developedby/Robo-Sugador/modelagem/hw/esq-motores.png

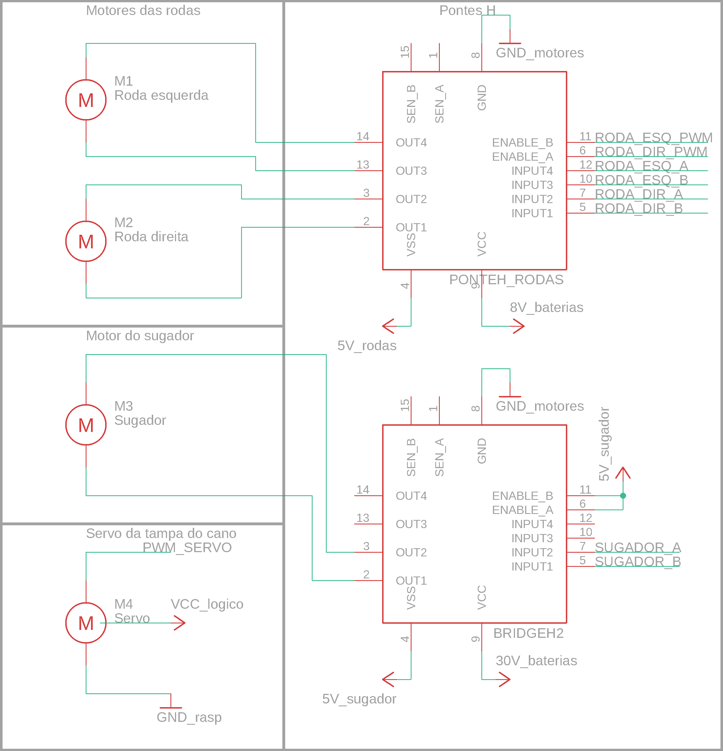
modelagem/hw/esq-motores.png
