developedby/Robo-Sugador/modelagem/hw/esq-rasp.png

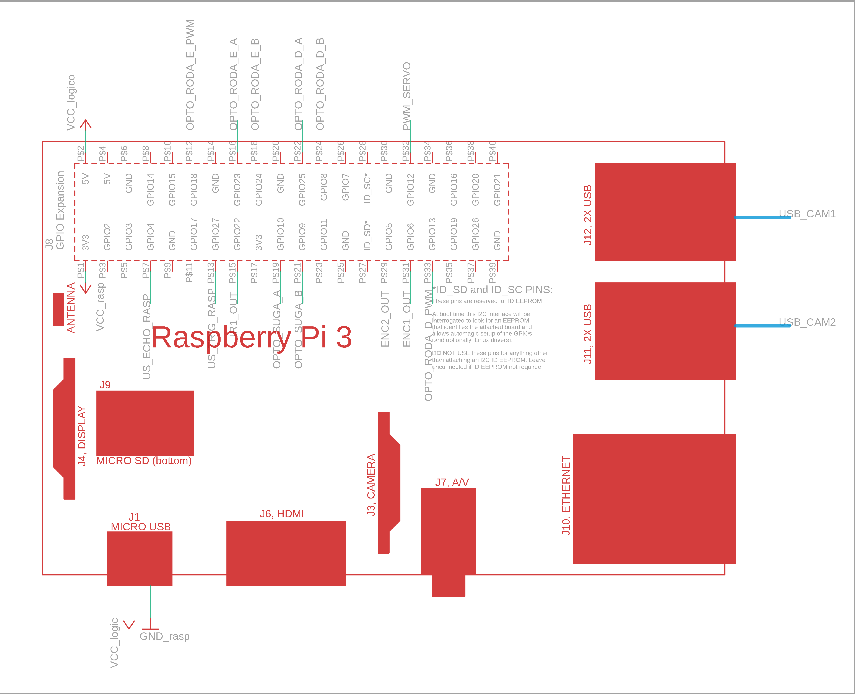
modelagem/hw/esq-rasp.png
