developedby/Robo-Sugador/modelagem/hw/esq-sensores.png

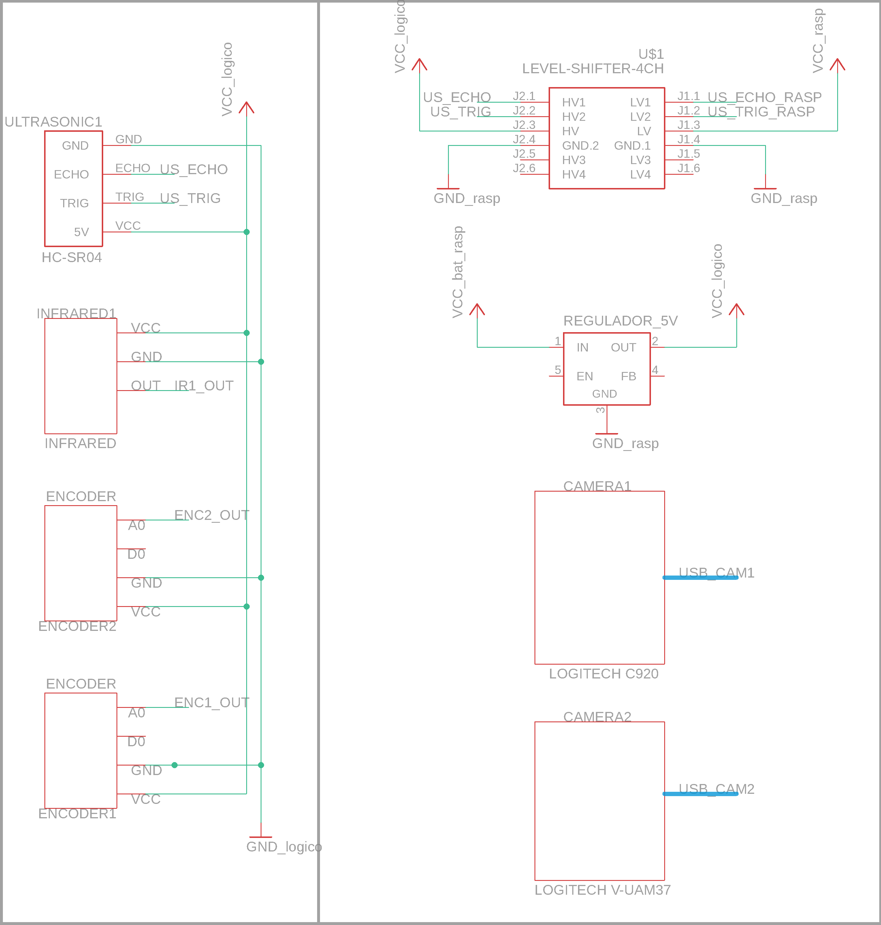
modelagem/hw/esq-sensores.png
