developedby/Robo-Sugador/modelagem/mecanica/45graus.jpg

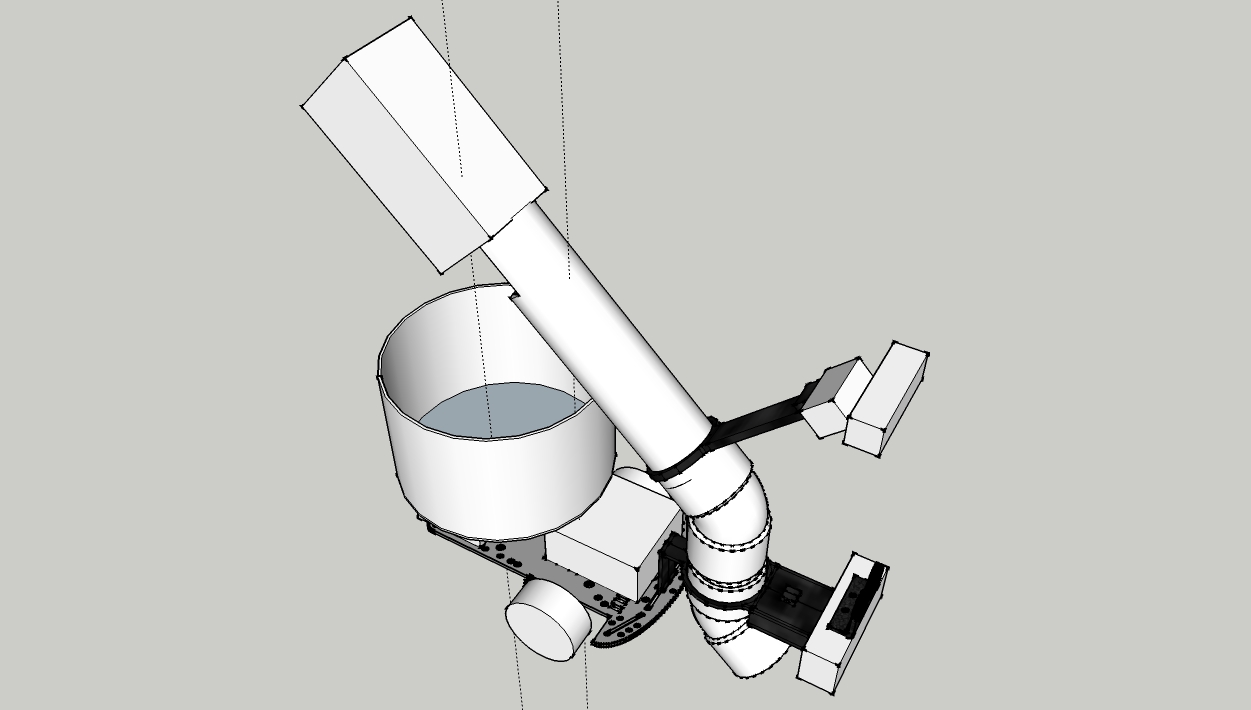
modelagem/mecanica/45graus.jpg
