developedby/Robo-Sugador/modelagem/mecanica/cima.jpg

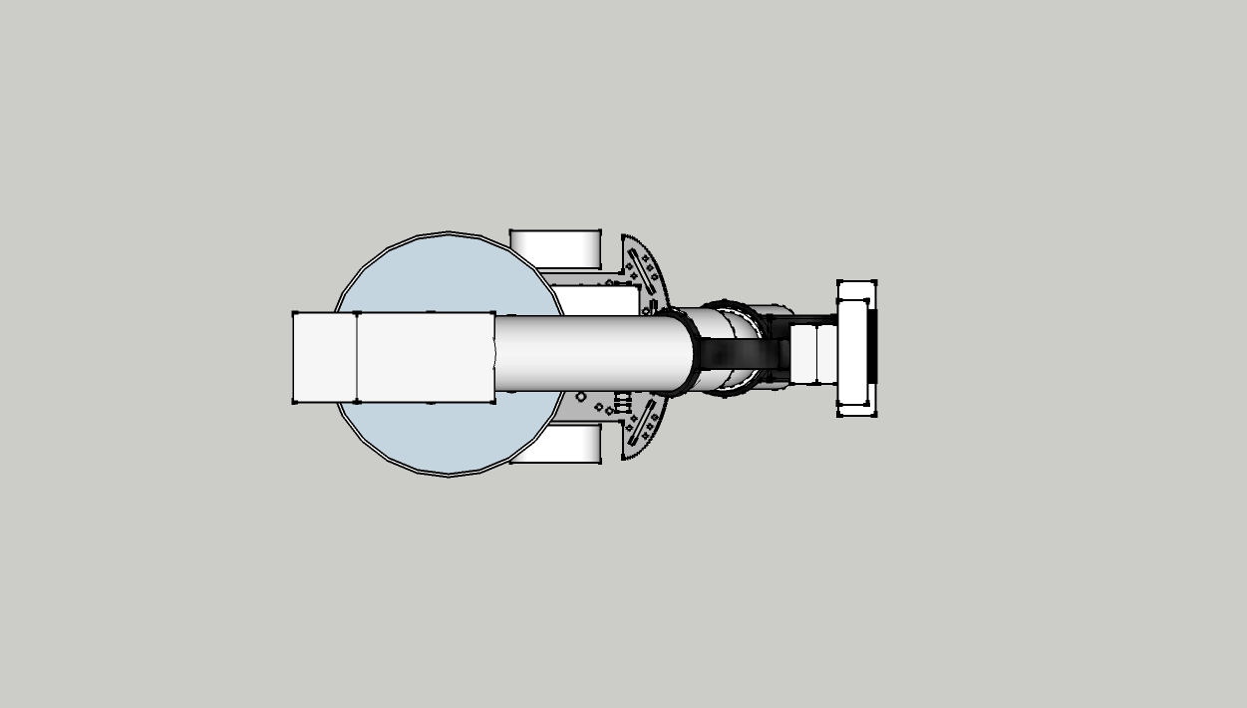
modelagem/mecanica/cima.jpg
