developedby/Robo-Sugador/modelagem/sistema/diagrama_superior.jpg

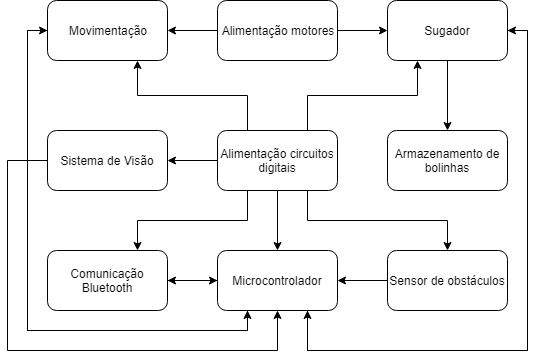
modelagem/sistema/diagrama_superior.jpg
