developedby/Robo-Sugador/modelagem/hw/robo_sugador.sch

## EAGLE design modelagem/hw/robo_sugador.sch (2018-11-27)

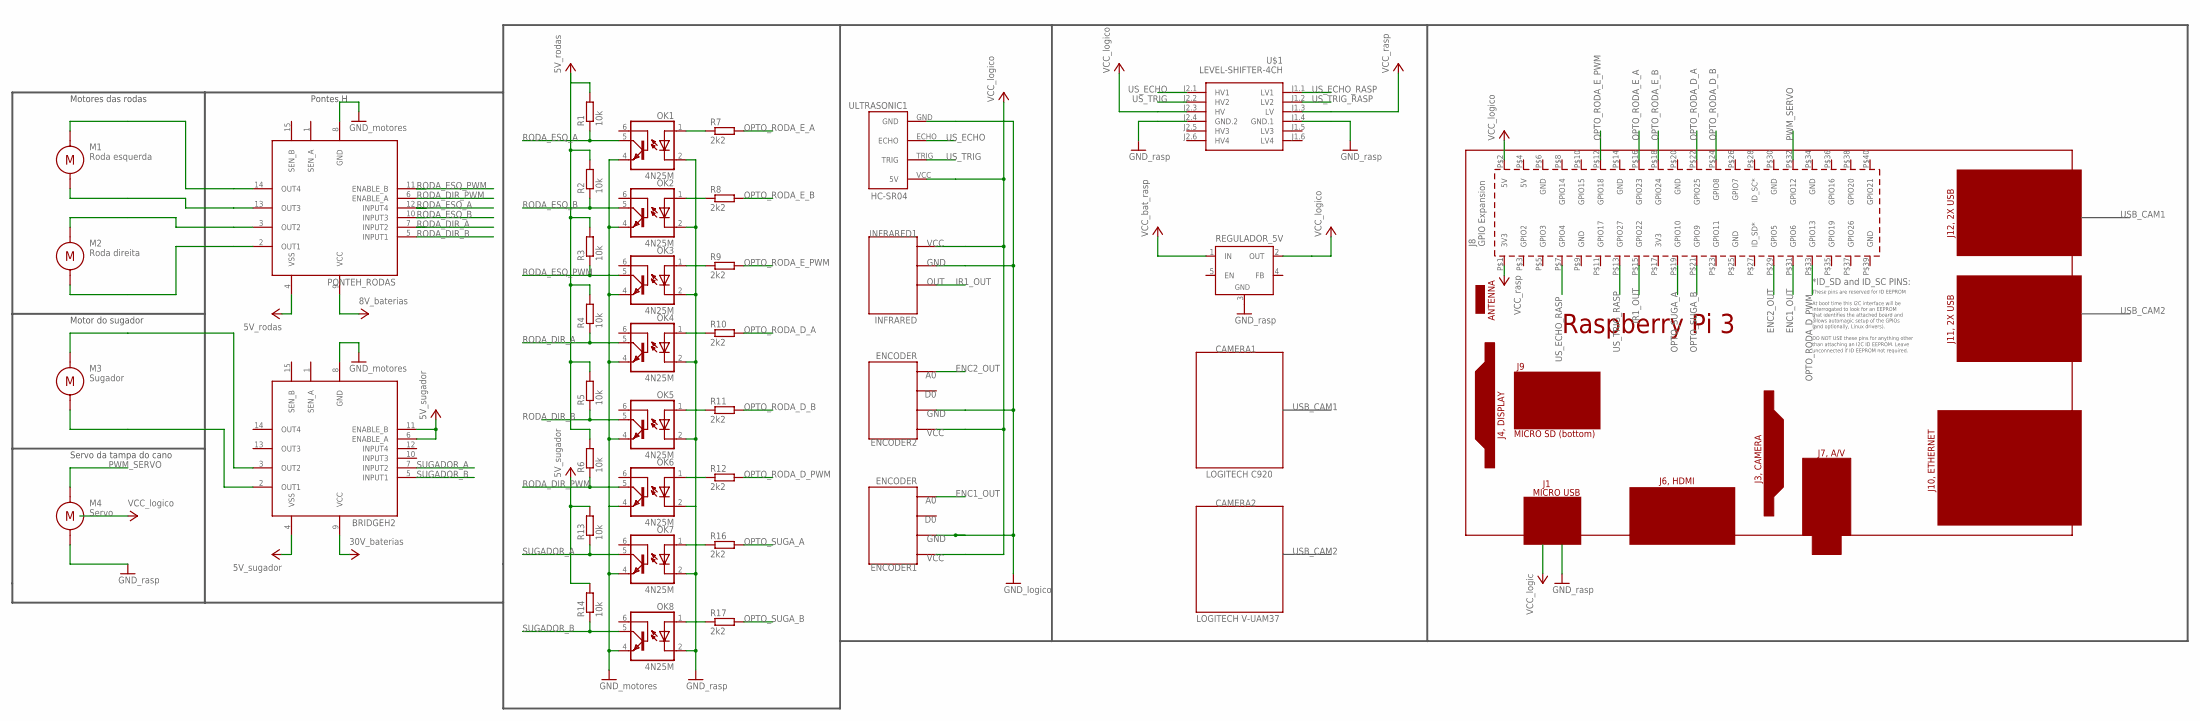
[picture p22: schematic robo_sugador.sch]

Parts:
BRIDGEH2: L298; MW-15
M1: Roda esquerda; 308-100
M2: Roda direita; 308-100
M3: Sugador; 308-100
M4: Servo; 308-100
OK1, OK2, OK3, OK4, OK5, OK6, OK7, OK8: 4N25M; DIL06
PCB1: RPI3RPI3; RPI3
PONTEH_RODAS: L298; MW-15
R1, R2, R3, R4, R5, R6, R13, R14: 10k; 0207/10
R7, R8, R9, R10, R11, R12, R16, R17: 2k2; 0207/10
REGULADOR_5V: LM2596TH; TO220-52
U$1: LEVEL-SHIFTER-4CH
ULTRASONIC1: HC-SR04; HC-SR04_FOOTPRINT

Connections:
ENC1_OUT: PCB1.P$31 (GPIO6)
ENC2_OUT: PCB1.P$29 (GPIO5)
GND: BRIDGEH2.8 (GND), M4.NEG, OK7.2 (C), OK7.4 (EMI), OK8.2 (C), OK8.4 (EMI), PONTEH_RODAS.8 (GND), REGULADOR_5V.3 (GND), U$1.J1.4 (GND.1), U$1.J2.4 (GND.2), ULTRASONIC1.GND
IR1_OUT: PCB1.P$15 (GPIO22)
unnamed: BRIDGEH2.3 (OUT2), M3.POS
unnamed: OK7.1 (A), R16.1
unnamed: BRIDGEH2.2 (OUT1), M3.NEG
unnamed: OK8.1 (A), R17.1
unnamed: OK1.4 (EMI), OK2.4 (EMI), OK3.4 (EMI), OK4.4 (EMI), OK5.4 (EMI), OK6.4 (EMI)
unnamed: M1.POS, PONTEH_RODAS.14 (OUT4)
unnamed: M1.NEG, PONTEH_RODAS.13 (OUT3)
unnamed: M2.POS, PONTEH_RODAS.3 (OUT2)
unnamed: M2.NEG, PONTEH_RODAS.2 (OUT1)
unnamed: OK1.2 (C), OK2.2 (C), OK3.2 (C), OK4.2 (C), OK5.2 (C), OK6.2 (C)
unnamed: OK1.1 (A), R7.1
unnamed: OK2.1 (A), R8.1
unnamed: OK3.1 (A), R9.1
unnamed: OK4.1 (A), R10.1
unnamed: OK5.1 (A), R11.1
unnamed: OK6.1 (A), R12.1
OPTO_RODA_D_A: PCB1.P$22 (GPIO25), R10.2
OPTO_RODA_D_B: PCB1.P$24 (GPIO8), R11.2
OPTO_RODA_D_PWM: PCB1.P$33 (GPIO13), R12.2
OPTO_RODA_E_A: PCB1.P$16 (GPIO23), R7.2
OPTO_RODA_E_B: PCB1.P$18 (GPIO24), R8.2
OPTO_RODA_E_PWM: PCB1.P$12 (GPIO18), R9.2
OPTO_SUGA_A: PCB1.P$19 (GPIO10), R16.2
OPTO_SUGA_B: PCB1.P$21 (GPIO9), R17.2
PWM_SERVO: M4.POS, PCB1.P$32 (GPIO12)
RODA_DIR_A: OK4.5 (COL), PONTEH_RODAS.7 (INPUT2), R4.1
RODA_DIR_B: OK5.5 (COL), PONTEH_RODAS.5 (INPUT1), R5.1
RODA_DIR_PWM: OK6.5 (COL), PONTEH_RODAS.6 (ENABLE_A), R6.1
RODA_ESQ_A: OK1.5 (COL), PONTEH_RODAS.12 (INPUT4), R1.1
RODA_ESQ_B: OK2.5 (COL), PONTEH_RODAS.10 (INPUT3), R2.1
RODA_ESQ_PWM: OK3.5 (COL), PONTEH_RODAS.11 (ENABLE_B), R3.1
SUGADOR_A: BRIDGEH2.7 (INPUT2), OK7.5 (COL), R13.1
SUGADOR_B: BRIDGEH2.5 (INPUT1), OK8.5 (COL), R14.1
US_ECHO: U$1.J2.1 (HV1), ULTRASONIC1.ECHO
US_ECHO_RASP: PCB1.P$7 (GPIO4), U$1.J1.1 (LV1)
US_TRIG: U$1.J2.2 (HV2), ULTRASONIC1.TRIG
US_TRIG_RASP: PCB1.P$13 (GPIO27), U$1.J1.2 (LV2)
VCC: BRIDGEH2.4 (VSS), BRIDGEH2.6 (ENABLE_A), BRIDGEH2.9 (VCC), BRIDGEH2.11 (ENABLE_B), PCB1.P$1 (3V3), PCB1.P$2 (5V), PONTEH_RODAS.4 (VSS), PONTEH_RODAS.9 (VCC), R1.2, R2.2, R3.2, R4.2, R5.2, R6.2, R13.2, R14.2, REGULADOR_5V.1 (IN), REGULADOR_5V.2 (OUT), U$1.J1.3 (LV), U$1.J2.3 (HV), ULTRASONIC1.VCC (5V)

Notes on the sheet:
ENCODER
ENCODER1
GND
VCC
ENCODER2
INFRARED
INFRARED1
OUT
LOGITECH C920
CAMERA1
LOGITECH V-UAM37
CAMERA2
Motores das rodas
Motor do sugador
Servo da tampa do cano
Pontes H
