developedby/Robo-Sugador/codigo/camera.py

# camera.py - Tira fotos com uma camera usb
# Informações sobre a licensa no arquivo LICENSE

import cv2

class Camera:
    def __init__ (self, port, resolution):
            self.resolution = resolution
            self.port = port
            self.capture = cv2.VideoCapture()
            self.capture.open(port)
            if not self.capture.isOpened():
                print("Warning - camera " + str(port) + " not opened correctly")
            self.capture.set(cv2.CAP_PROP_FRAME_WIDTH, resolution['width'])
            self.capture.set(cv2.CAP_PROP_FRAME_HEIGHT, resolution['height'])

    def image (self):
        if not self.capture.isOpened():
            self.capture.open(self.port)
        retval, image = self.capture.read()
        return image

    def close (self):
        self.capture.release()
