developedby/Robo-Sugador/codigo/testes/teste_imagem3.py

# Teste 3 - Tenta aproximar por poligono


import cv2
import numpy as np

def nothing(x):
    pass

cam = cv2.VideoCapture()
cam.open(0)
cam.set(cv2.CAP_PROP_FRAME_WIDTH, 1280)
cam.set(cv2.CAP_PROP_FRAME_HEIGHT, 720)

# Create a window
cv2.namedWindow('Treshed')

# create trackbars for treshold change
cv2.createTrackbar('Treshold','Treshed',0,255,nothing)


while(1):

    ret, img = cam.read()

    # Convert to gray
    gray = cv2.cvtColor(img, cv2.COLOR_BGR2GRAY)

    # get current positions of four trackbars
    r = cv2.getTrackbarPos('Treshold','Treshed')

    # Thresholding the gray image
    ret,gray_threshed = cv2.threshold(gray,r,255,cv2.THRESH_BINARY)

    # Blur an image
    bilateral_filtered_image = cv2.bilateralFilter(gray_threshed, 5, 175, 175)

    # Detect edges
    edge_detected_image = cv2.Canny(bilateral_filtered_image, 75, 200)

    # Find contours
    _, contours, _= cv2.findContours(edge_detected_image, cv2.RETR_TREE, cv2.CHAIN_APPROX_SIMPLE)

    contour_list = []
    for contour in contours:
        # approximte for circles
        approx = cv2.approxPolyDP(contour,0.01*cv2.arcLength(contour,True),True)
        area = cv2.contourArea(contour)
        if ((len(approx) > 8) & (area > 30) ):
            contour_list.append(contour)

    # Draw contours on the original image
    cv2.drawContours(img, contour_list,  -1, (255,0,0), 2)

    # there is an outer boundary and inner boundary for each eadge, so contours double
    print('Number of found circles: {}'.format(int(len(contour_list)/2)))

    #Displaying the results
    cv2.imshow('Objects Detected', img)
    cv2.imshow("Treshed", gray_threshed)

    # ESC to break
    k = cv2.waitKey(1) & 0xFF
    if k == 27:
        break

# close all open windows
cv2.destroyAllWindows()
